na103/ar3/Kicad/ARIII/ARIII.kicad_sch

## KiCad design Kicad/ARIII/ARIII.kicad_sch (2024-10-04)

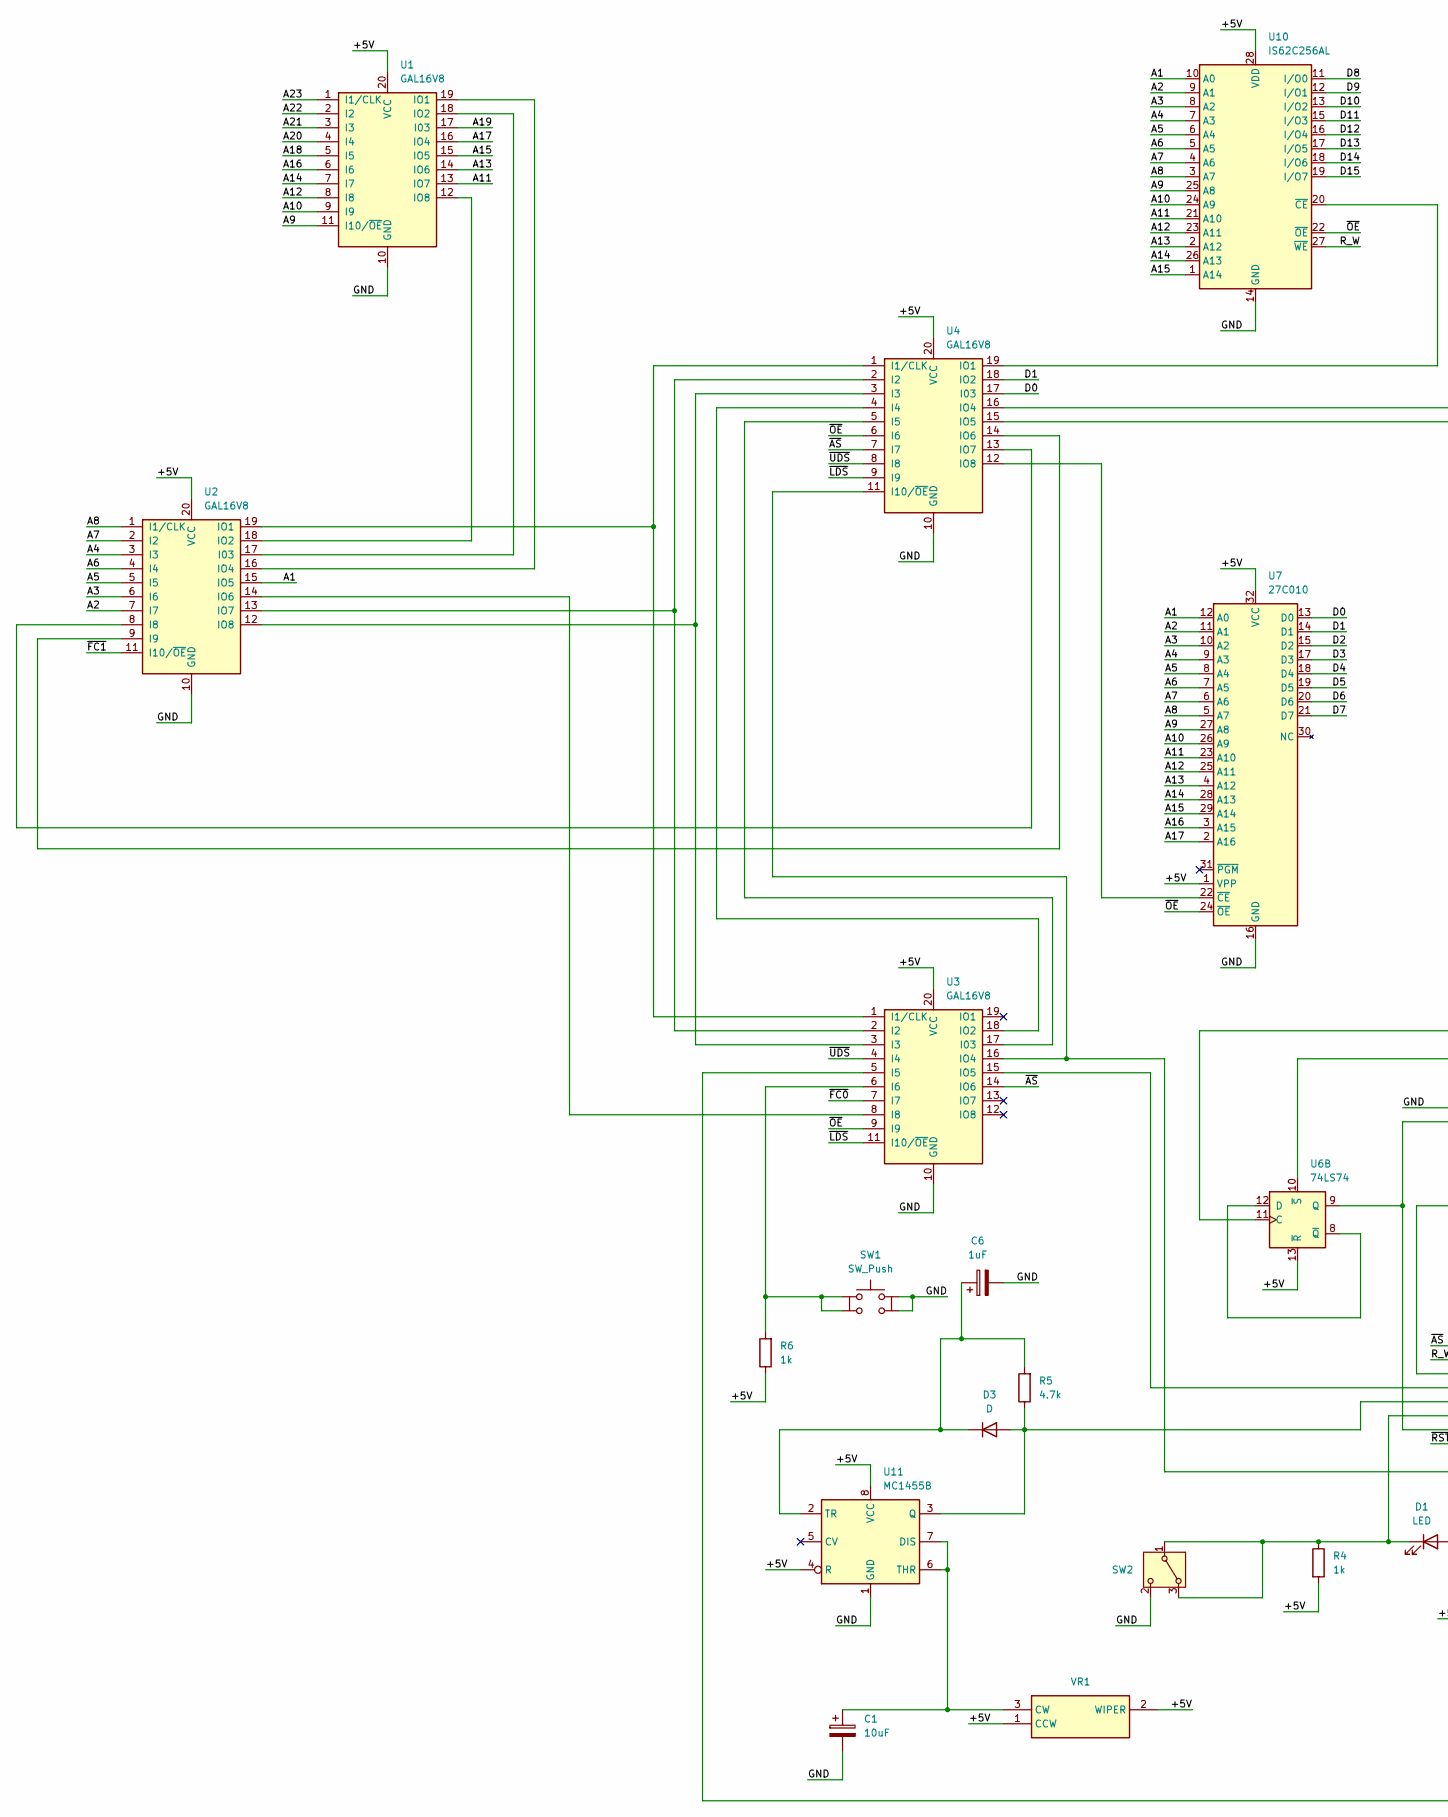
[picture p7: schematic ARIII.kicad_sch, part in row 1, column 1]

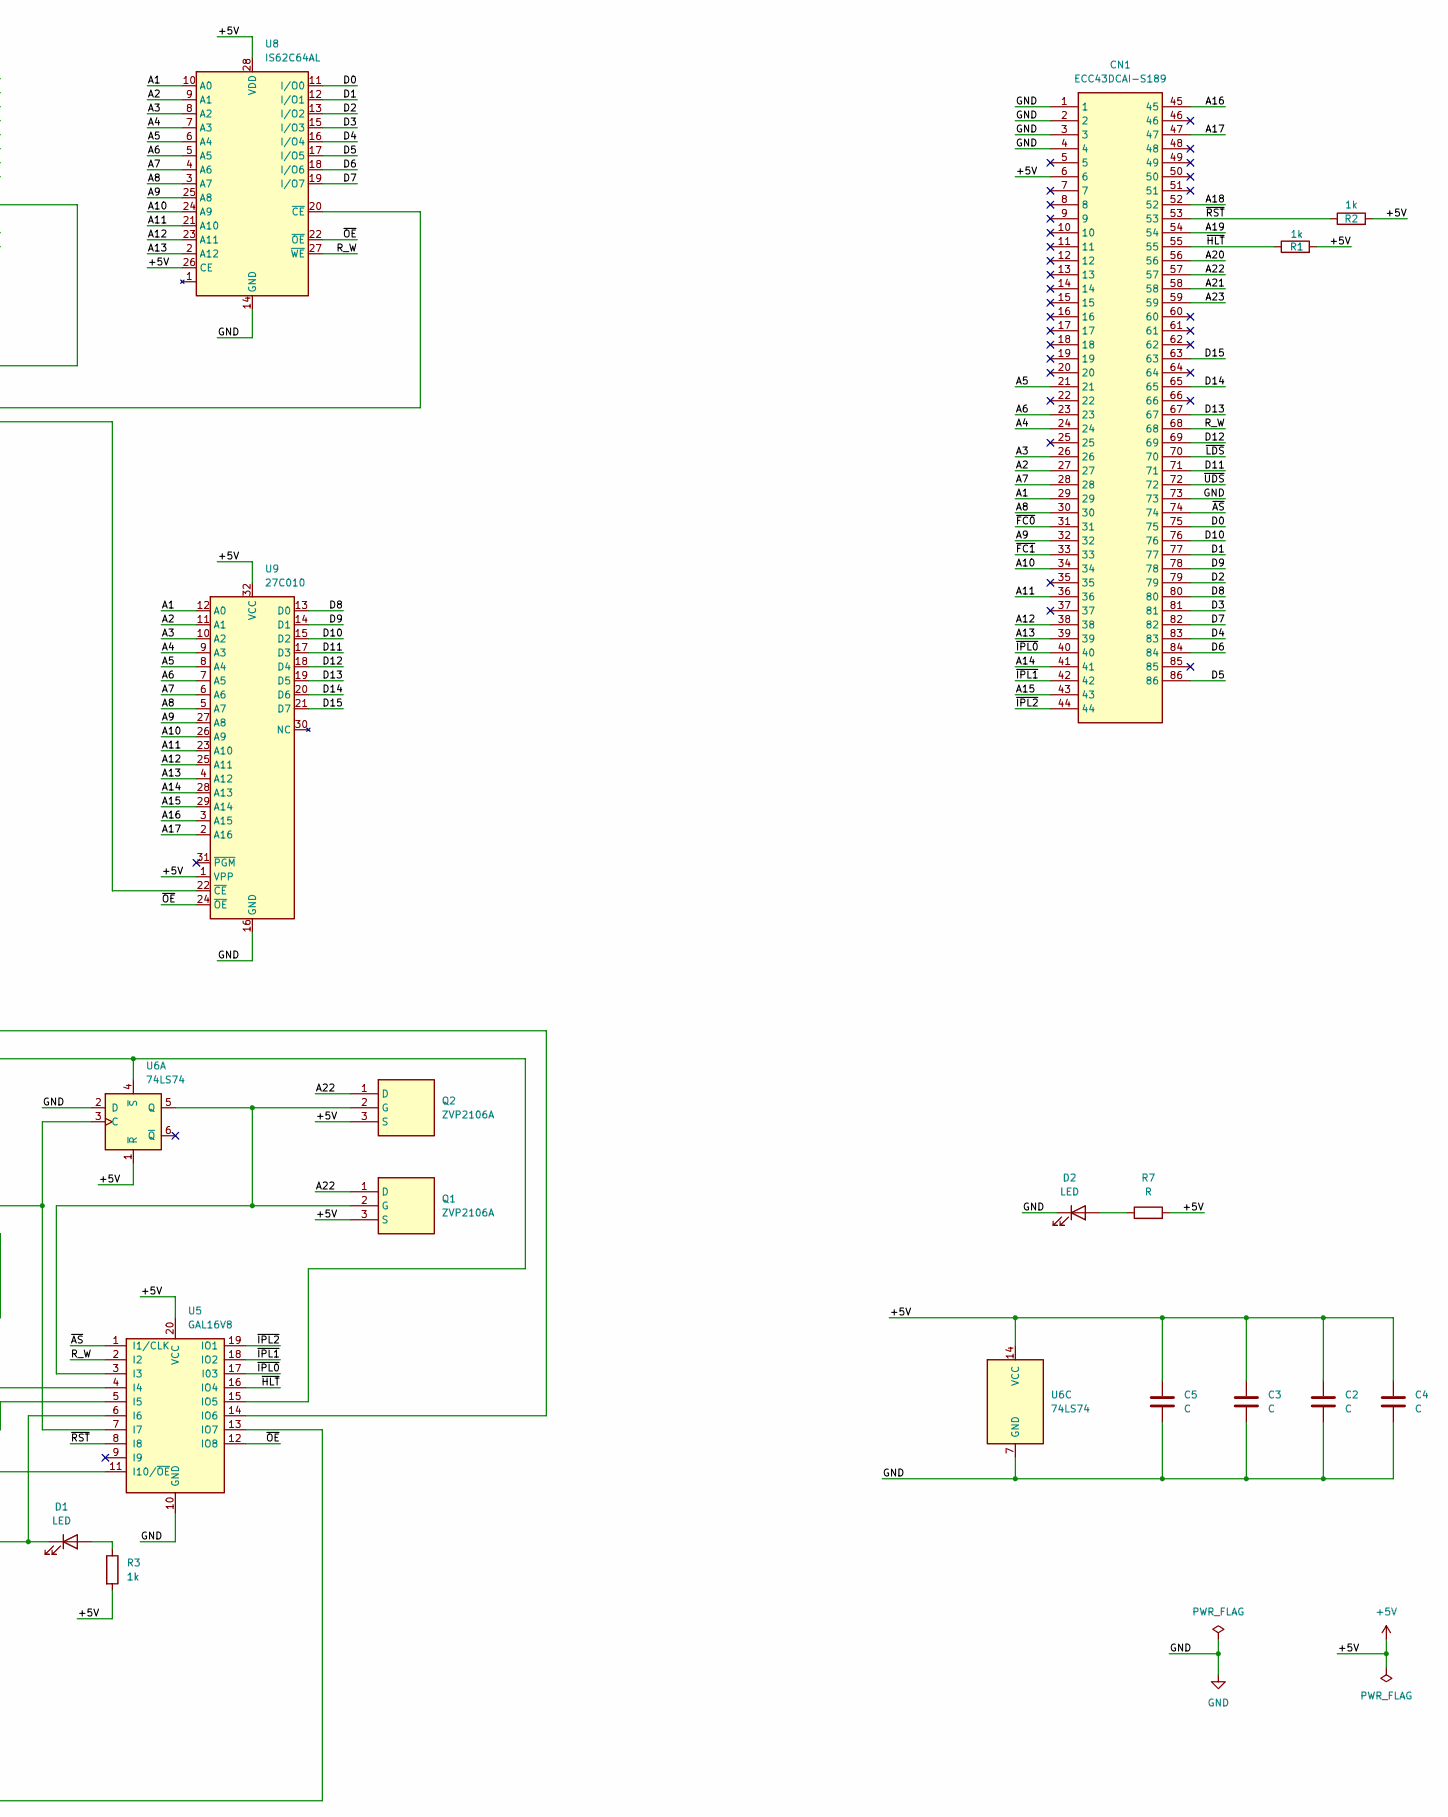
[picture p8: schematic ARIII.kicad_sch, part in row 1, column 2]

Parts:
C1: 10uF; CP_Radial_D5.0mm_P2.50mm
C2, C3, C4, C5: C; C_1206_3216Metric_Pad1.33x1.80mm_HandSolder
C6: 1uF; CP_Radial_D5.0mm_P2.50mm
CN1: ECC43DCAI-S189; ECC43DCAIS189; Manufacturer_Part_Number ECC43DCAI-S189
D1, D2: LED; LED_D3.0mm
D3: D; D_1206_3216Metric_Pad1.42x1.75mm_HandSolder
Q1, Q2: ZVP2106A; TO-92_Inline_Wide; Mouser Part Number 522-ZVP2106A
R1, R2, R3, R4, R6: 1k; R_1206_3216Metric_Pad1.30x1.75mm_HandSolder
R5: 4.7k; R_1206_3216Metric_Pad1.30x1.75mm_HandSolder
R7: R; R_1206_3216Metric_Pad1.30x1.75mm_HandSolder
SW1: SW_Push; SW_Push_2P1T_Toggle_CK_PVA1xxH1xxxxxxV2
SW2: SW_Wuerth_450301014042; SW_Slide-03_Wuerth-WS-SLTV_10x2.5x6.4_P2.54mm
U1, U2, U3, U4, U5: GAL16V8; PLCC-20
U6: 74LS74; SO-14_Hyrbrid
U7, U9: 27C010; PLCC-32_11.4x14.0mm_P1.27mm
U8: IS62C64AL; SOP-28_MIL330_ALL
U10: IS62C256AL; SOP-28_MIL330_ALL
U11: MC1455B; SOIC-8_3.9x4.9mm_P1.27mm
VR1: 3386F-1-103LF; 3386F1153; Mouser Part Number 652-3386F-1-103LF

Connections:
+5V: C2.1, C3.1, C4.2, C5.1, CN1.6, Q1.3 (S), Q2.3 (S), R1.2, R2.2, R3.2, R4.2, R6.1, R7.2, U1.20 (VCC), U2.20 (VCC), U3.20 (VCC), U4.20 (VCC), U5.20 (VCC), U6.1 (~R), U6.13 (~R), U6.14 (VCC), U7.1 (VPP), U7.32 (VCC), U8.26 (CE), U8.28 (VDD), U9.1 (VPP), U9.32 (VCC), U10.28 (VDD), U11.4 (R), U11.8 (VCC), VR1.1 (CCW), VR1.2 (WIPER)
A1: CN1.29, U2.15 (IO5), U7.12 (A0), U8.10 (A0), U9.12 (A0), U10.10 (A0)
A2: CN1.27, U2.7 (I7), U7.11 (A1), U8.9 (A1), U9.11 (A1), U10.9 (A1)
A3: CN1.26, U2.6 (I6), U7.10 (A2), U8.8 (A2), U9.10 (A2), U10.8 (A2)
A4: CN1.24, U2.3 (I3), U7.9 (A3), U8.7 (A3), U9.9 (A3), U10.7 (A3)
A5: CN1.21, U2.5 (I5), U7.8 (A4), U8.6 (A4), U9.8 (A4), U10.6 (A4)
A6: CN1.23, U2.4 (I4), U7.7 (A5), U8.5 (A5), U9.7 (A5), U10.5 (A5)
A7: CN1.28, U2.2 (I2), U7.6 (A6), U8.4 (A6), U9.6 (A6), U10.4 (A6)
A8: CN1.30, U2.1 (I1/CLK), U7.5 (A7), U8.3 (A7), U9.5 (A7), U10.3 (A7)
A9: CN1.32, U1.11 (I10/~OE), U7.27 (A8), U8.25 (A8), U9.27 (A8), U10.25 (A8)
A10: CN1.34, U1.9 (I9), U7.26 (A9), U8.24 (A9), U9.26 (A9), U10.24 (A9)
A11: CN1.36, U1.13 (IO7), U7.23 (A10), U8.21 (A10), U9.23 (A10), U10.21 (A10)
A12: CN1.38, U1.8 (I8), U7.25 (A11), U8.23 (A11), U9.25 (A11), U10.23 (A11)
A13: CN1.39, U1.14 (IO6), U7.4 (A12), U8.2 (A12), U9.4 (A12), U10.2 (A12)
A14: CN1.41, U1.7 (I7), U7.28 (A13), U9.28 (A13), U10.26 (A13)
A15: CN1.43, U1.15 (IO5), U7.29 (A14), U9.29 (A14), U10.1 (A14)
A16: CN1.45, U1.6 (I6), U7.3 (A15), U9.3 (A15)
A17: CN1.47, U1.16 (IO4), U7.2 (A16), U9.2 (A16)
A18: CN1.52, U1.5 (I5)
A19: CN1.54, U1.17 (I03)
A20: CN1.56, U1.4 (I4)
A21: CN1.58, U1.3 (I3)
A22: CN1.57, Q1.1 (D), Q2.1 (D), U1.2 (I2)
A23: CN1.59, U1.1 (I1/CLK)
D0: CN1.75, U4.17 (I03), U7.13 (D0), U8.11 (I/O0)
D1: CN1.77, U4.18 (IO2), U7.14 (D1), U8.12 (I/O1)
D2: CN1.79, U7.15 (D2), U8.13 (I/O2)
D3: CN1.81, U7.17 (D3), U8.15 (I/O3)
D4: CN1.83, U7.18 (D4), U8.16 (I/O4)
D5: CN1.86, U7.19 (D5), U8.17 (I/O5)
D6: CN1.84, U7.20 (D6), U8.18 (I/O6)
D7: CN1.82, U7.21 (D7), U8.19 (I/O7)
D8: CN1.80, U9.13 (D0), U10.11 (I/O0)
D9: CN1.78, U9.14 (D1), U10.12 (I/O1)
D10: CN1.76, U9.15 (D2), U10.13 (I/O2)
D11: CN1.71, U9.17 (D3), U10.15 (I/O3)
D12: CN1.69, U9.18 (D4), U10.16 (I/O4)
D13: CN1.67, U9.19 (D5), U10.17 (I/O5)
D14: CN1.65, U9.20 (D6), U10.18 (I/O6)
D15: CN1.63, U9.21 (D7), U10.19 (I/O7)
GND: C1.2, C2.2, C3.2, C4.1, C5.2, C6.2, CN1.1, CN1.2, CN1.3, CN1.4, CN1.73, D2.1 (K), SW1.2, SW1.4, SW2.2 (C), U1.10 (GND), U2.10 (GND), U3.10 (GND), U4.10 (GND), U5.10 (GND), U6.2 (D), U6.7 (GND), U7.16 (GND), U8.14 (GND), U9.16 (GND), U10.14 (GND), U11.1 (GND)
unnamed: C1.1, U11.6 (THR), U11.7 (DIS), VR1.3 (CW)
unnamed: C6.1, D3.1 (K), R5.2, U11.2 (TR)
unnamed: D1.1 (K), R4.1, SW2.1 (B), SW2.3 (A), U5.6 (I6)
unnamed: D1.2 (A), R3.1
unnamed: D2.2 (A), R7.1
unnamed: D3.2 (A), R5.1, U5.5 (I5), U11.3 (Q)
unnamed: Q1.2 (G), Q2.2 (G), U5.3 (I3), U6.5 (Q)
unnamed: R6.2, SW1.1, SW1.3, U3.6 (I6)
unnamed: U1.12 (IO8), U2.18 (IO2)
unnamed: U1.18 (IO2), U2.17 (I03)
unnamed: U1.19 (IO1), U2.16 (IO4)
unnamed: U2.8 (I8), U4.13 (IO7)
unnamed: U2.9 (I9), U4.14 (IO6)
unnamed: U2.12 (IO8), U3.3 (I3), U4.3 (I3)
unnamed: U2.13 (IO7), U3.2 (I2), U4.2 (I2)
unnamed: U2.14 (IO6), U3.8 (I8)
unnamed: U2.19 (IO1), U3.1 (I1/CLK), U4.1 (I1/CLK)
unnamed: U3.5 (I5), U5.13 (IO7)
unnamed: U3.15 (IO5), U5.4 (I4)
unnamed: U3.16 (IO4), U4.11 (I10/~OE), U5.11 (I10/~OE)
unnamed: U3.17 (I03), U4.5 (I5)
unnamed: U3.18 (IO2), U4.4 (I4)
unnamed: U4.12 (IO8), U7.22 (~CE)
unnamed: U4.15 (IO5), U9.22 (~CE)
unnamed: U4.16 (IO4), U8.20 (~CE)
unnamed: U5.7 (I7), U6.3 (C), U6.9 (Q)
unnamed: U5.14 (IO6), U6.11 (C)
unnamed: U5.15 (IO5), U6.4 (~S), U6.10 (~S)
unnamed: U6.8 (~Q), U6.12 (D)
unnamed: U4.19 (IO1), U10.20 (~CE)
R_W: CN1.68, U5.2 (I2), U8.27 (~WE), U10.27 (~WE)
~AS: CN1.74, U3.14 (IO6), U4.7 (I7), U5.1 (I1/CLK)
~FC0: CN1.31, U3.7 (I7)
~FC1: CN1.33, U2.11 (I10/~OE)
~HLT: CN1.55, R1.1, U5.16 (IO4)
~IPL0: CN1.40, U5.17 (I03)
~IPL1: CN1.42, U5.18 (IO2)
~IPL2: CN1.44, U5.19 (IO1)
~LDS: CN1.70, U3.11 (I10/~OE), U4.9 (I9)
~OE: U3.9 (I9), U4.6 (I6), U5.12 (IO8), U7.24 (~OE), U8.22 (~OE), U9.24 (~OE), U10.22 (~OE)
~RST: CN1.53, R2.1, U5.8 (I8)
~UDS: CN1.72, U3.4 (I4), U4.8 (I8)
